MOSH-Insa-Toulouse/2023-2024-4GP-The-Bao---Fadoua/MIT_app/Start BTN.png

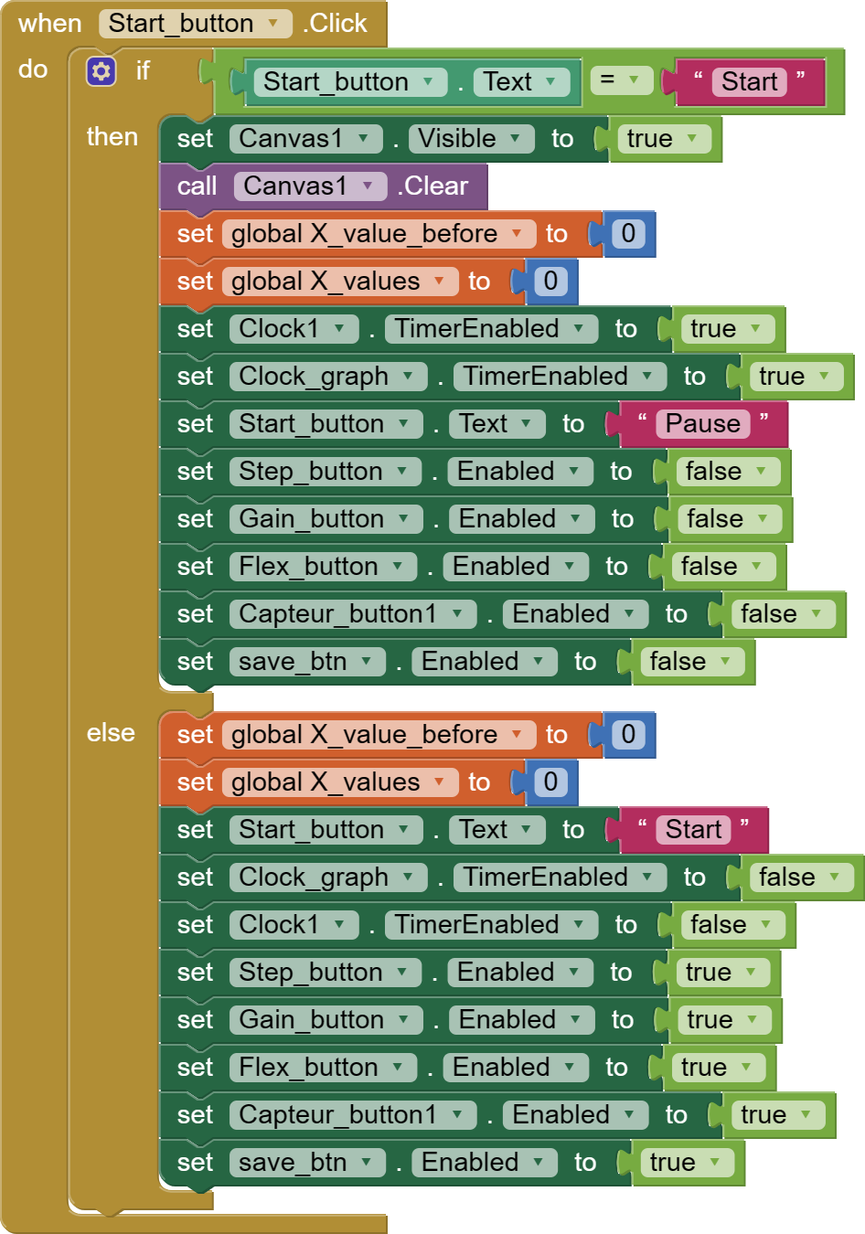
MIT_app/Start BTN.png
