MOSH-Insa-Toulouse/2023-2024-4GP-The-Bao---Fadoua/3d model/rotary-encoder-1.snapshot.8/rotary encoder step files/Step Files/mtg flange.stp

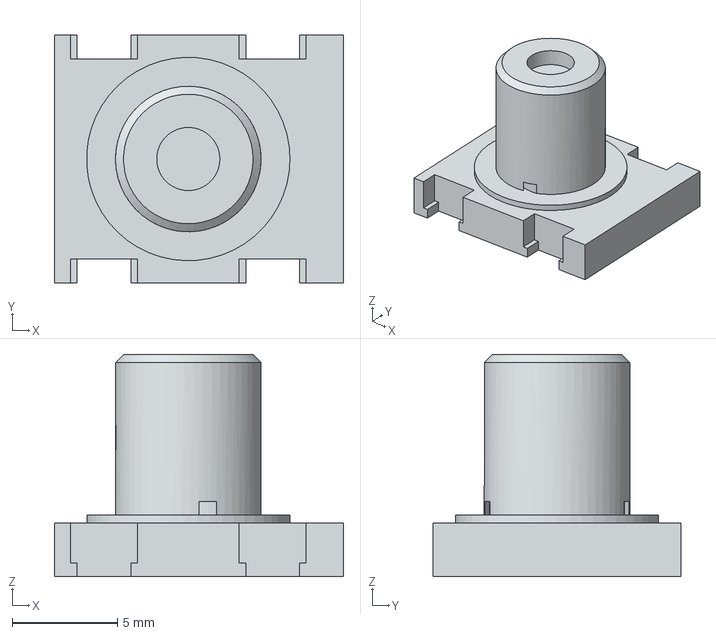
[picture p38: CAD file, 2024-06-07]
3d model/rotary-encoder-1.snapshot.8/rotary encoder step files/Step Files/mtg flange.stp
13.7 x 11.8 x 10.5 mm
