MOSH-Insa-Toulouse/2023-2024-4GP-The-Bao---Fadoua/3d model/rotary-encoder-1.snapshot.8/rotary encoder step files/Step Files/90d pin_header.stp

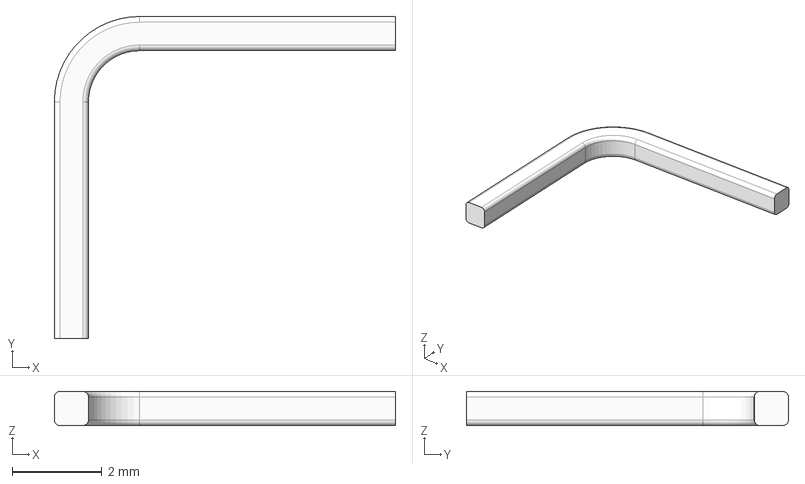
[picture p39: CAD file, 2024-06-07]
3d model/rotary-encoder-1.snapshot.8/rotary encoder step files/Step Files/90d pin_header.stp
7.62 x 7.19 x 0.762 mm
