MOSH-Insa-Toulouse/2023-2024-4GP-The-Bao---Fadoua/3d model/rotary-encoder-1.snapshot.8/rotary encoder step files/Step Files/pins_encoder body_2.stp

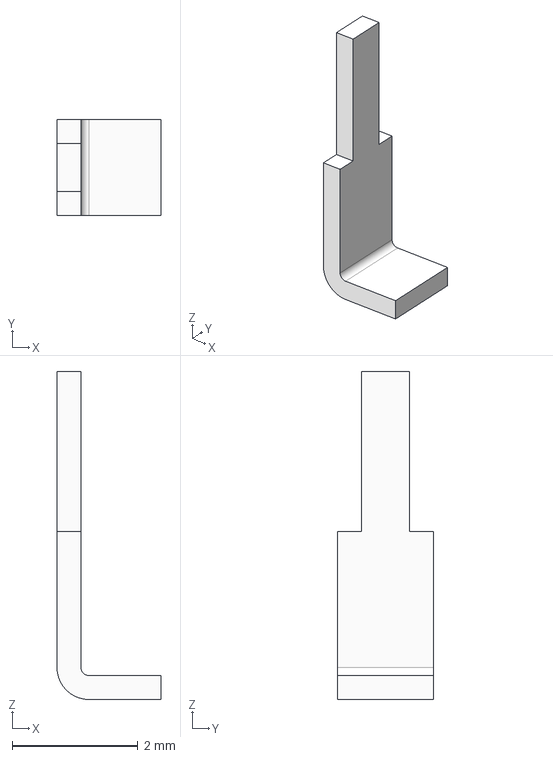
[picture p40: CAD file, 2024-06-07]
3d model/rotary-encoder-1.snapshot.8/rotary encoder step files/Step Files/pins_encoder body_2.stp
1.65 x 1.52 x 5.21 mm
